sungo/crkbd-curvy-sandwich/images/acrylic/IMG_0199.jpeg

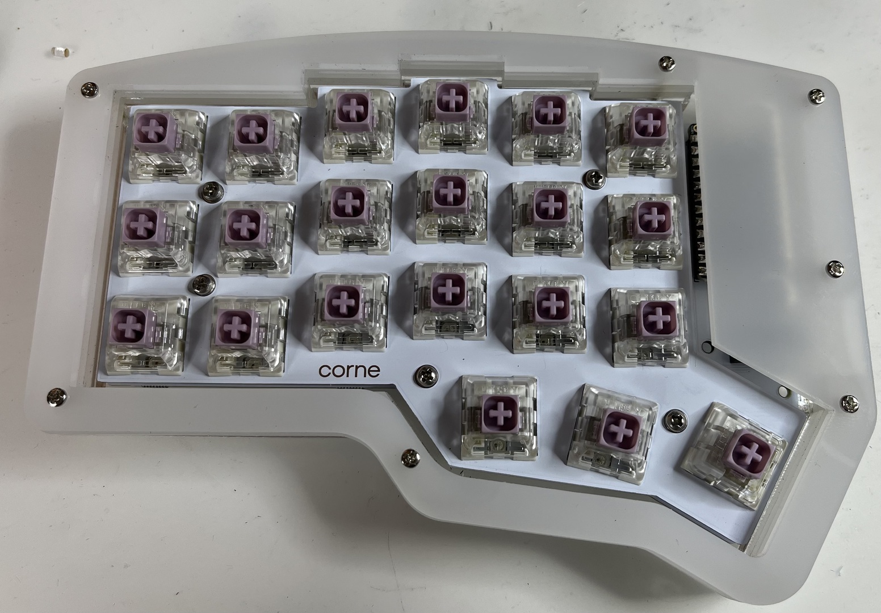
images/acrylic/IMG_0199.jpeg
