sungo/crkbd-curvy-sandwich/images/acrylic/IMG_0203.jpeg

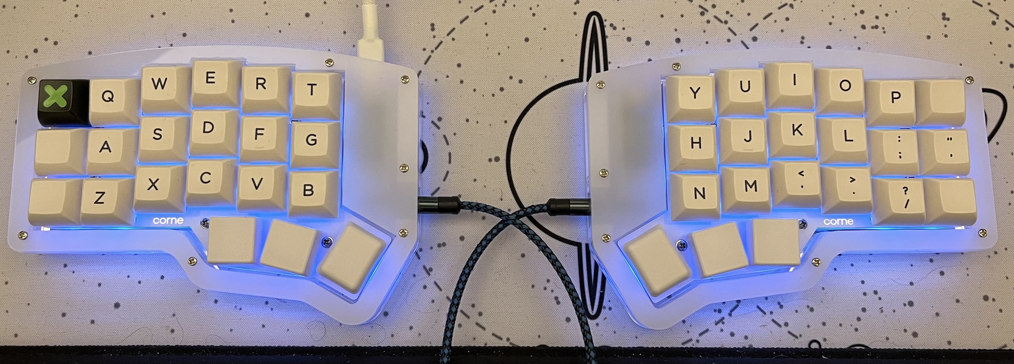
images/acrylic/IMG_0203.jpeg
