sungo/crkbd-curvy-sandwich/images/acrylic/IMG_0204.jpeg

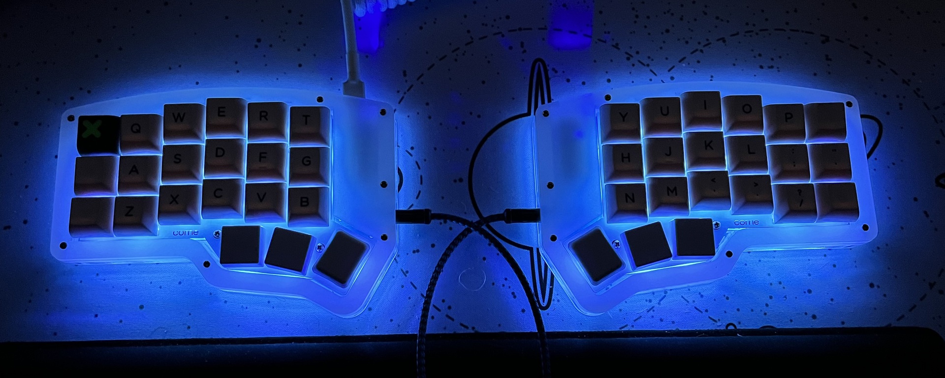
images/acrylic/IMG_0204.jpeg
